sameer5504/ESP32-Micromouse/Battery Holder.jpg

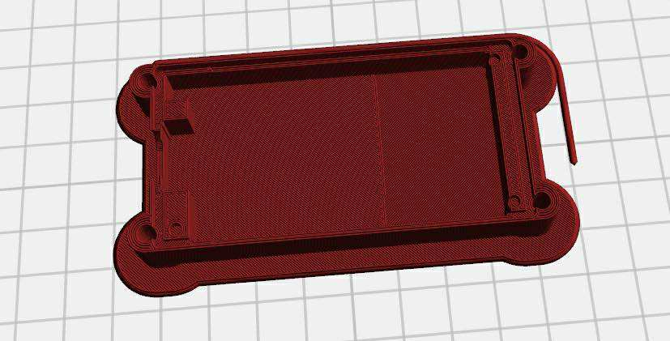
Battery Holder.jpg
