sameer5504/ESP32-Micromouse/ESP32 microcontroller.jpg

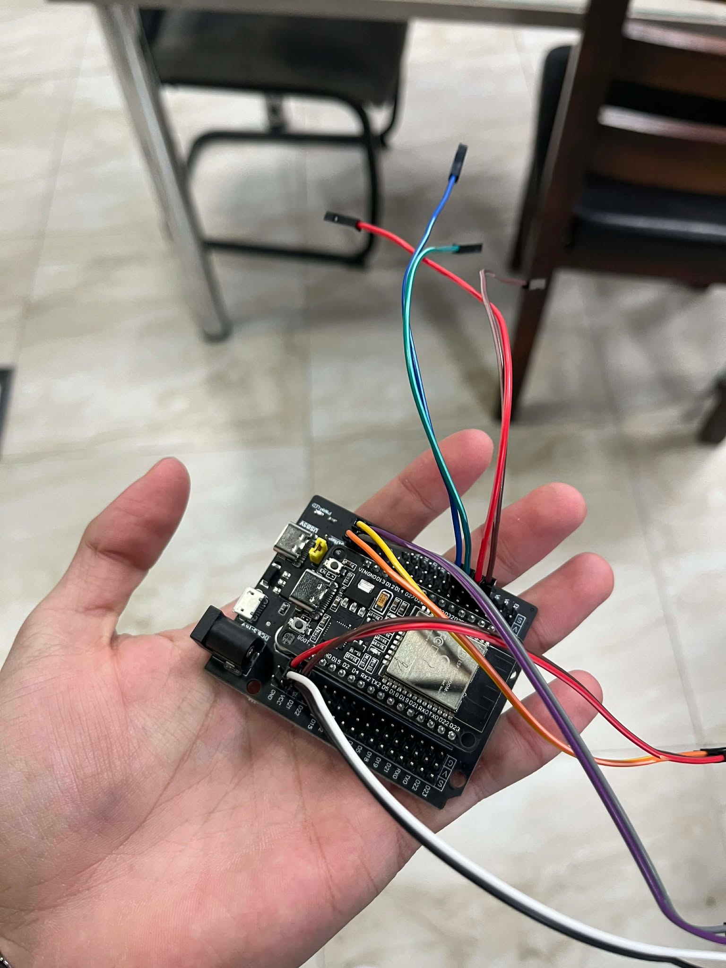
ESP32 microcontroller.jpg
