sameer5504/ESP32-Micromouse/Top Base.jpg

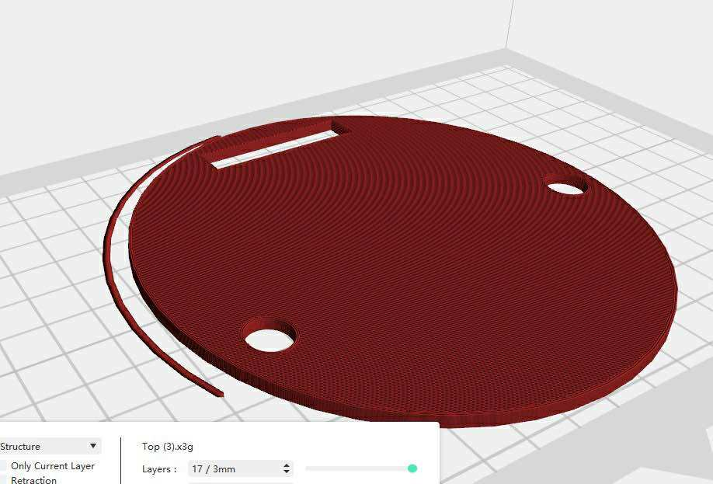
Top Base.jpg
